Snahkx/Person_Tracker/hardware/drawings/piVertical.SLDPRT

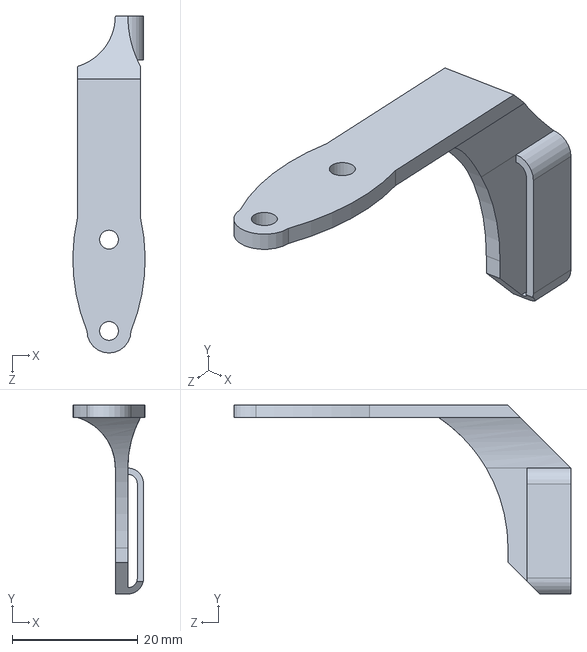
[picture p13: CAD file, 2026-02-10]
hardware/drawings/piVertical.SLDPRT
11.5 x 30.0 x 53.5 mm
